mvacoss/DIY-Vacuum-tube-amp-head/Class A tube amp.kicad_sch

## KiCad design Class A tube amp.kicad_sch (2026-05-17)

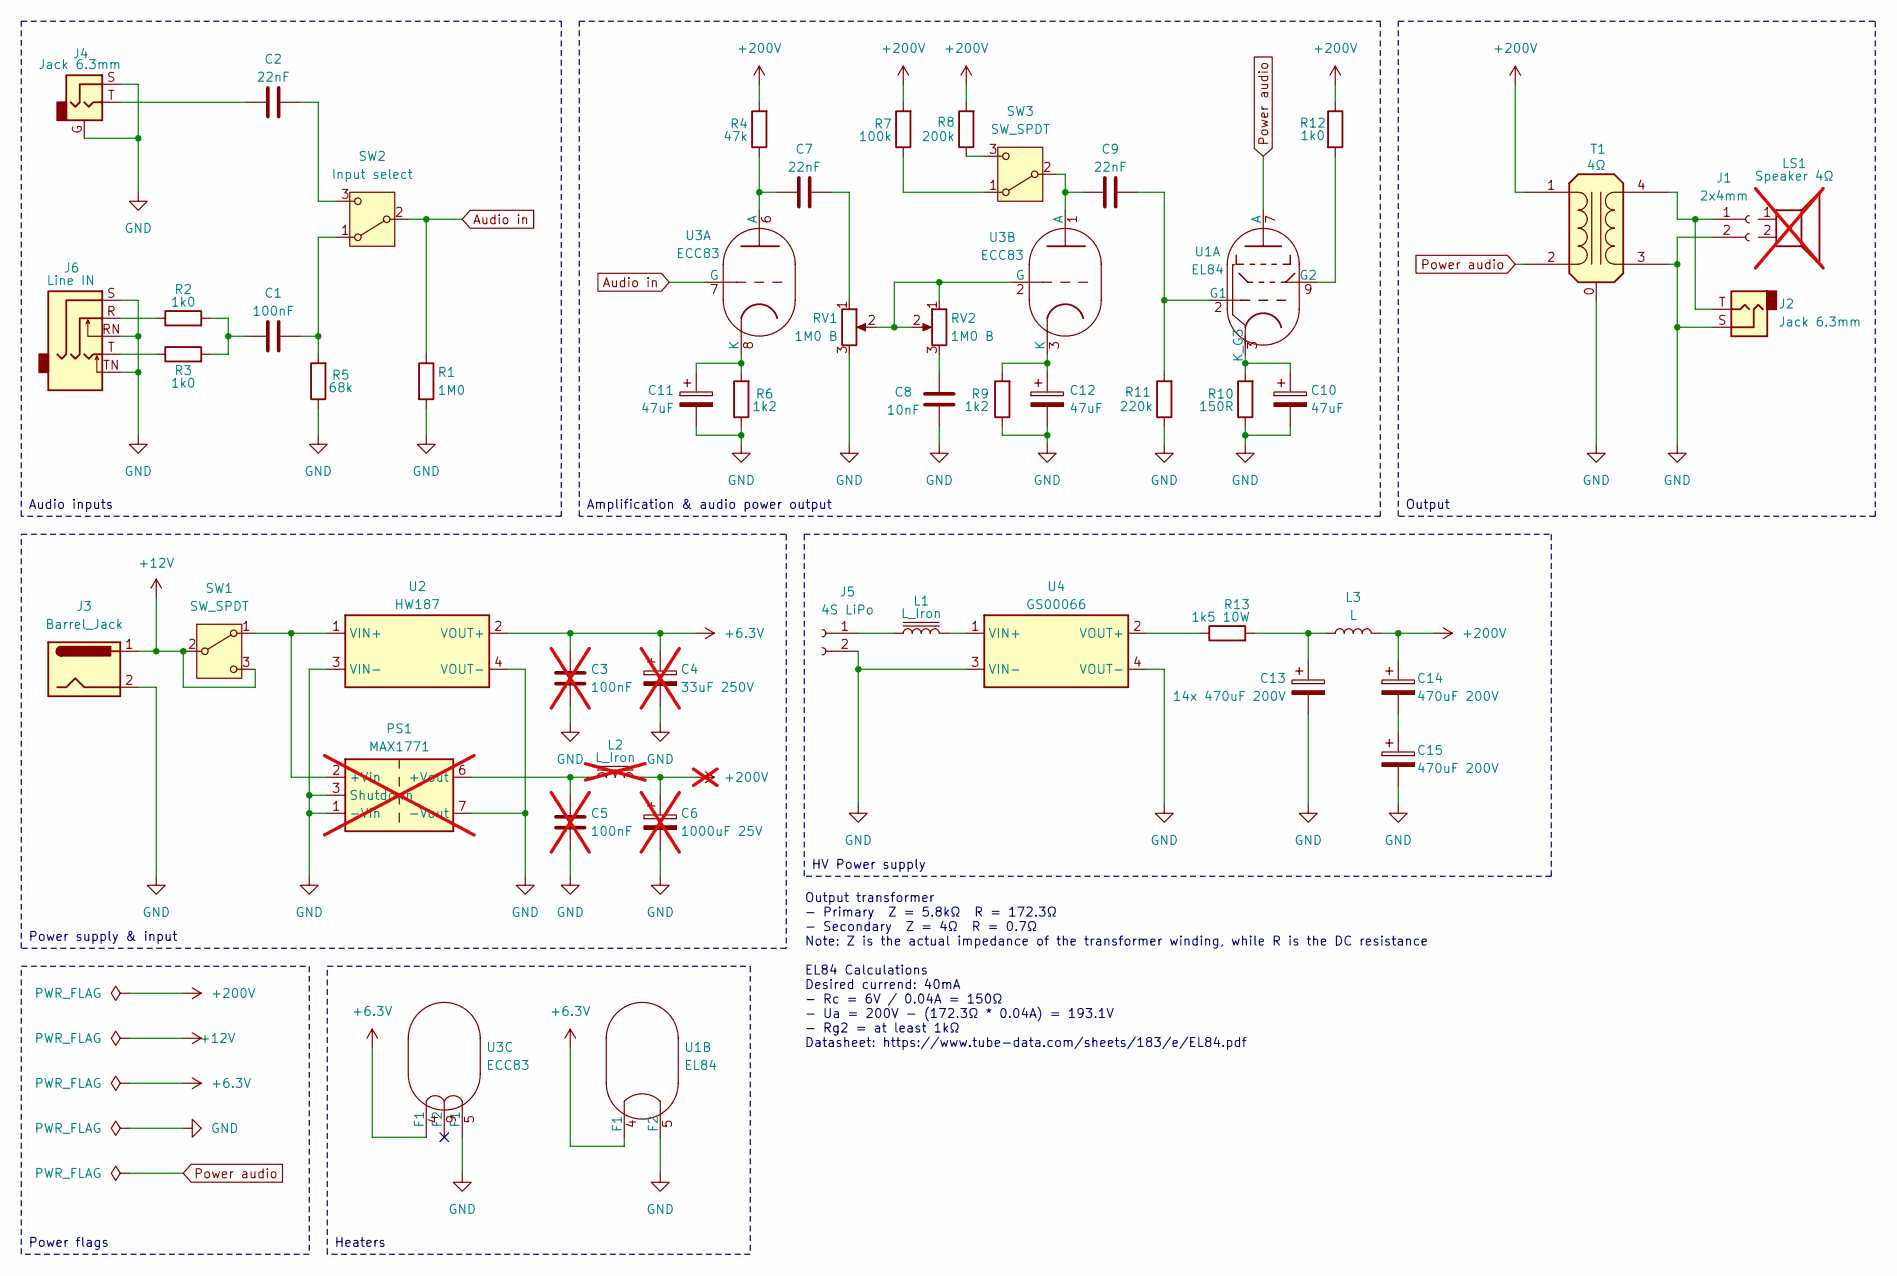
[picture p2: schematic Class A tube amp.kicad_sch]

Parts:
C1: 100nF
C2, C7, C9: 22nF
C3, C5: 100nF; not fitted
C4: 33uF 250V; not fitted
C6: 1000uF 25V; not fitted
C8: 10nF
C10, C11, C12: 47uF
C13: 14x 470uF 200V
C14, C15: 470uF 200V
J1: 2x4mm
J2, J4: Jack 6.3mm
J3: Barrel_Jack
J5: 4S LiPo
J6: Line IN; Jack_3.5mm_CUI_SJ1-3525N_Horizontal
L1: L_Iron
L2: L_Iron; not fitted
L3: L
LS1: Speaker 4Ω; not fitted
PS1: MAX1771; Converter_DCDC_XP_POWER-ITxxxxxS_THT; not fitted
R1: 1M0; R_Axial_DIN0207_L6.3mm_D2.5mm_P10.16mm_Horizontal
R2, R3, R12: 1k0; R_Axial_DIN0207_L6.3mm_D2.5mm_P10.16mm_Horizontal
R4: 47k; R_Axial_DIN0207_L6.3mm_D2.5mm_P10.16mm_Horizontal
R5: 68k; R_Axial_DIN0207_L6.3mm_D2.5mm_P10.16mm_Horizontal
R6, R9: 1k2; R_Axial_DIN0207_L6.3mm_D2.5mm_P10.16mm_Horizontal
R7: 100k; R_Axial_DIN0207_L6.3mm_D2.5mm_P10.16mm_Horizontal
R8: 200k; R_Axial_DIN0207_L6.3mm_D2.5mm_P10.16mm_Horizontal
R10: 150R; R_Axial_DIN0207_L6.3mm_D2.5mm_P10.16mm_Horizontal
R11: 220k; R_Axial_DIN0207_L6.3mm_D2.5mm_P10.16mm_Horizontal
R13: 1k5 10W; R_Axial_DIN0207_L6.3mm_D2.5mm_P10.16mm_Horizontal
RV1, RV2: 1M0 B
SW1, SW3: SW_SPDT
SW2: Input select
T1: 4Ω
U1: EL84; Valve_Noval_P
U2: HW187; TO-263-5_TabPin3
U3: ECC83; Valve_Noval_P
U4: GS00066; TO-263-5_TabPin3

Connections:
+6.3V: C3.1, C4.1, U1.4 (F1), U2.2 (VOUT+), U3.4 (F1)
+12V: J3.1, SW1.2 (B), SW1.3 (C)
+200V: C6.1, C14.1, L2.2, L3.2, R4.2, R7.2, R8.2, R12.1, T1.1 (AA)
Audio in: R1.1, SW2.2 (B), U3.7 (G)
GND: C3.2, C4.2, C5.2, C6.2, C8.1, C10.2, C11.2, C12.2, C13.2, C15.2, J1.2, J2.S, J3.2, J4.G, J4.S, J5.2, J6.RN, J6.S, J6.TN, PS1.1 (-Vin), PS1.3 (Shutdown), PS1.7 (-Vout), R1.2, R5.1, R6.1, R9.1, R10.1, R11.1, RV1.3, T1.0, T1.3 (SA), U1.5 (F2), U2.3 (VIN-), U2.4 (VOUT-), U3.5 (F1), U4.3 (VIN-), U4.4 (VOUT-)
unnamed: C1.1, R2.2, R3.2
unnamed: C1.2, R5.2, SW2.1 (A)
unnamed: C2.1, J4.T
unnamed: C2.2, SW2.3 (C)
unnamed: C5.1, L2.1, PS1.6 (+Vout)
unnamed: C7.1, R4.1, U3.6 (A)
unnamed: C7.2, RV1.1
unnamed: C8.2, RV2.3
unnamed: C9.1, SW3.2 (B), U3.1 (A)
unnamed: C9.2, R11.2, U1.2 (G1)
unnamed: C10.1, R10.2, U1.3 (K_G3)
unnamed: C11.1, R6.2, U3.8 (K)
unnamed: C12.1, R9.2, U3.3 (K)
unnamed: C13.1, L3.1, R13.2
unnamed: C14.2, C15.1
unnamed: J1.1, J2.T, T1.4 (SB)
unnamed: J5.1, L1.1
unnamed: J6.R, R2.1
unnamed: J6.T, R3.1
unnamed: L1.2, U4.1 (VIN+)
unnamed: PS1.2 (+Vin), SW1.1 (A), U2.1 (VIN+)
unnamed: R7.1, SW3.1 (A)
unnamed: R8.1, SW3.3 (C)
unnamed: R12.2, U1.9 (G2)
unnamed: R13.1, U4.2 (VOUT+)
unnamed: RV1.2, RV2.1, RV2.2, U3.2 (G)
Power audio: T1.2 (AB), U1.7 (A)

Notes on the sheet:
Output transformer - Primary Z = 5.8kΩ R = 172.3Ω - Secondary Z = 4Ω R = 0.7Ω Note: Z is the actual impedance of the transformer winding, while R is the DC resistance EL84 Calculations Desired currend: 40mA - Rc = 6V / 0.04A = 150Ω - Ua = 200V - (172.3Ω * 0.04A) = 193.1V - Rg2 = at least 1kΩ Datash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
Heaters
Output
Amplification & audio power output
Power flags
Power supply & input
Audio inputs
HV Power supply
